ddraig68k/hardware/ddraig-libs/CAD/Connectors/35RAPC4BHN2.step

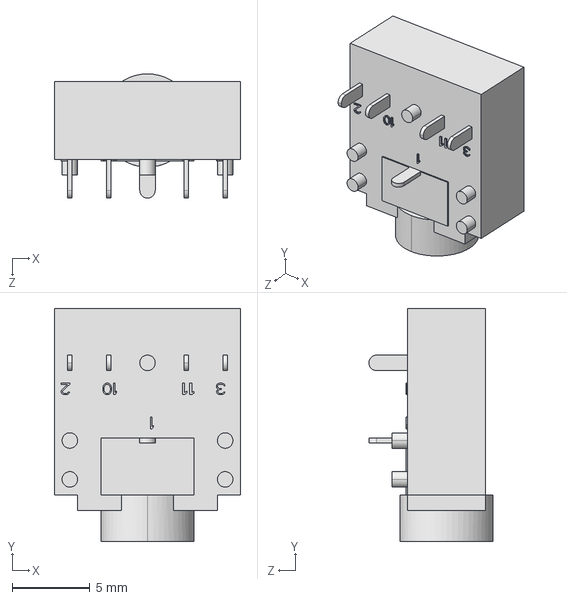
[picture p23: CAD file, 2024-05-17]
ddraig-libs/CAD/Connectors/35RAPC4BHN2.step
12.0 x 15.0 x 8.00 mm
