ddraig68k/hardware/ddraig-libs/CAD/IC Sockets/plcc44_p1-27_l16-66_w16-66.stp

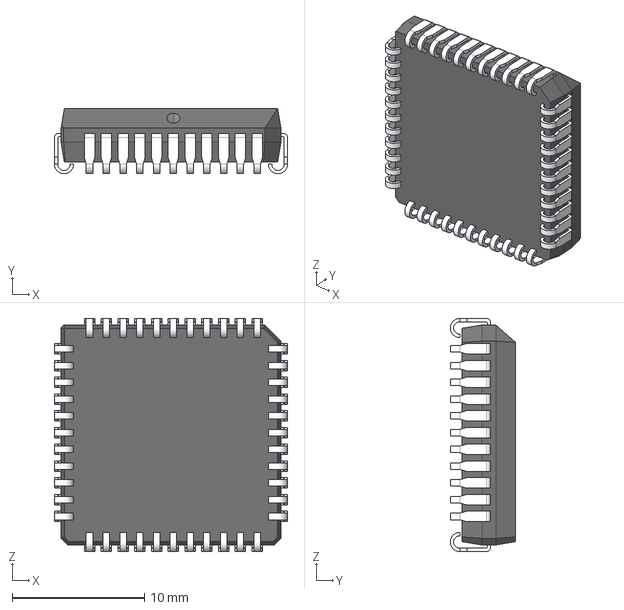
[picture p24: CAD file, 2021-05-24]
ddraig-libs/CAD/IC Sockets/plcc44_p1-27_l16-66_w16-66.stp
17.6 x 4.96 x 17.6 mm
