ddraig68k/hardware/ddraig-libs/CAD/Jumpers/Jumper3-yellow.step

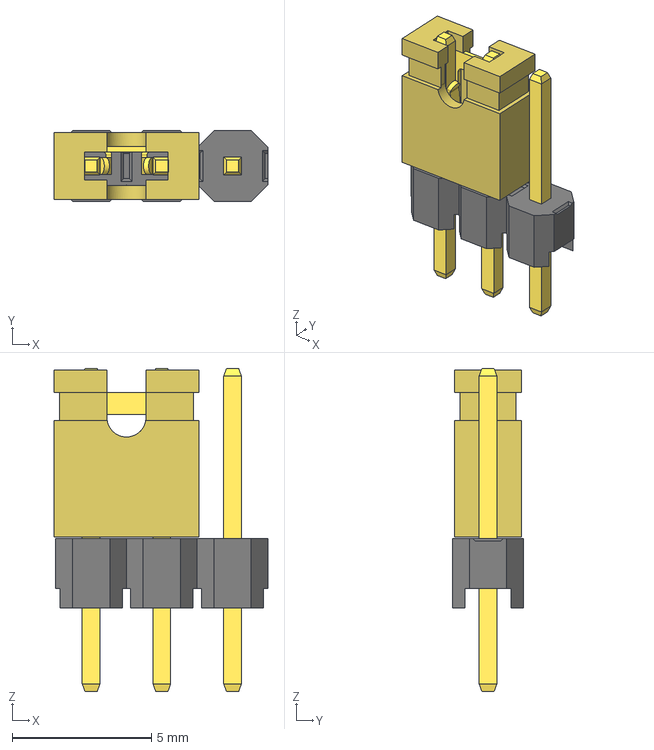
[picture p25: CAD file, 2023-10-23]
ddraig-libs/CAD/Jumpers/Jumper3-yellow.step
7.68 x 2.54 x 11.6 mm
