ddraig68k/hardware/ddraig-libs/CAD/Connectors/HARTING 09651626812.stp

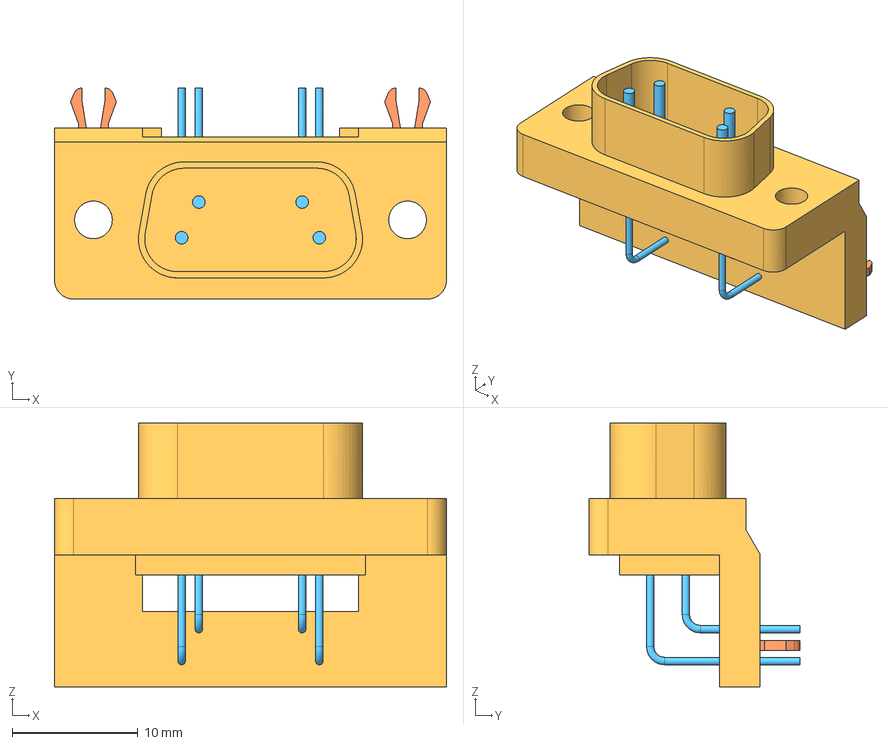
[picture p26: CAD file, 2022-08-17]
ddraig-libs/CAD/Connectors/HARTING 09651626812.stp
31.2 x 16.8 x 21.0 mm
