ddraig68k/hardware/ddraig-libs/CAD/IC Sockets/plcc84_p1-27_l29-41_w29-41.stp

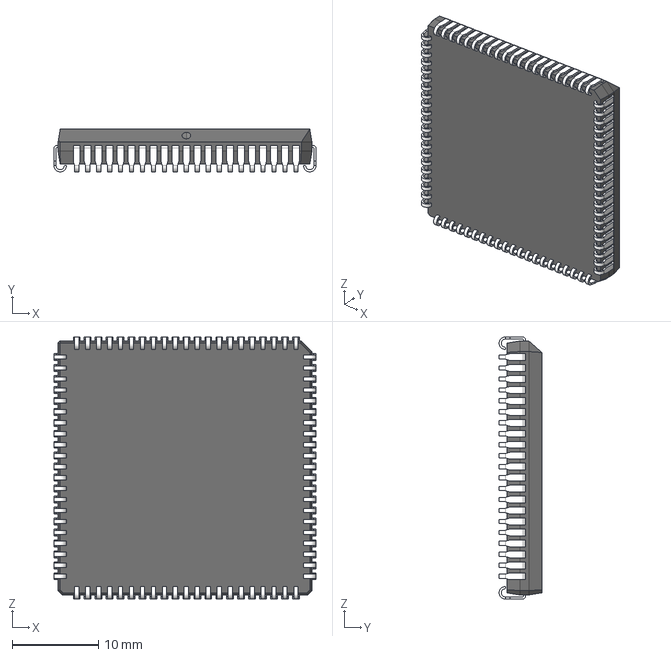
[picture p27: CAD file, 2021-05-19]
ddraig-libs/CAD/IC Sockets/plcc84_p1-27_l29-41_w29-41.stp
30.4 x 4.96 x 30.4 mm
