ddraig68k/hardware/ddraig-libs/CAD/Components/M2022TXW41-DA.stp

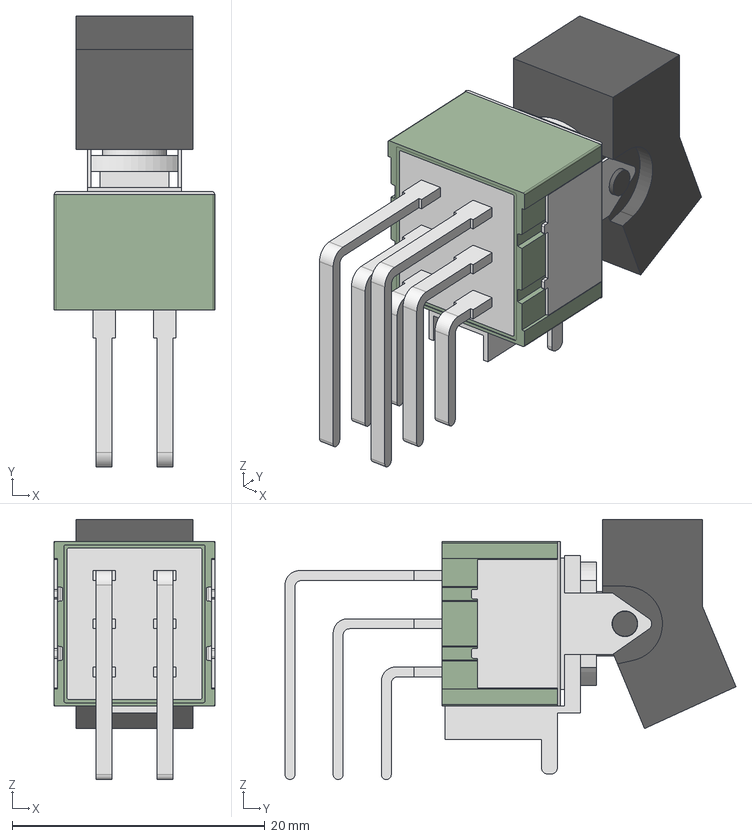
[picture p28: CAD file, 2021-09-19]
ddraig-libs/CAD/Components/M2022TXW41-DA.stp
12.7 x 35.7 x 20.6 mm
_M202TX241-switch
_M202TX-cover
_M202TX41-cover-t
_M2012TXW41-DA-terminal41
_AT4148-2A-rocker
_M202241W-terminal
