ddraig68k/hardware/ddraig-libs/CAD/Connectors/CUI_DEVICES_UP2-AH-1-TH.step

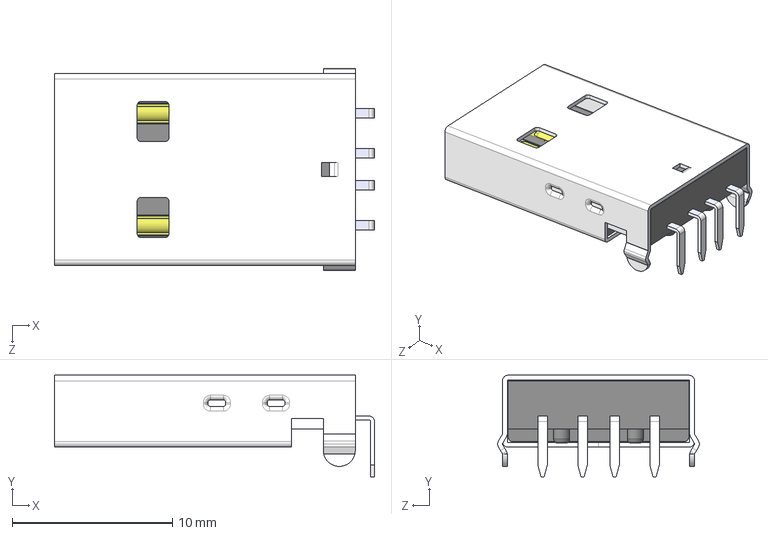
[picture p29: CAD file, 2021-10-08]
ddraig-libs/CAD/Connectors/CUI_DEVICES_UP2-AH-1-TH.step
20.0 x 6.35 x 12.6 mm
