ddraig68k/hardware/ddraig-libs/CAD/IC Sockets/PLCC44 Socket.igs

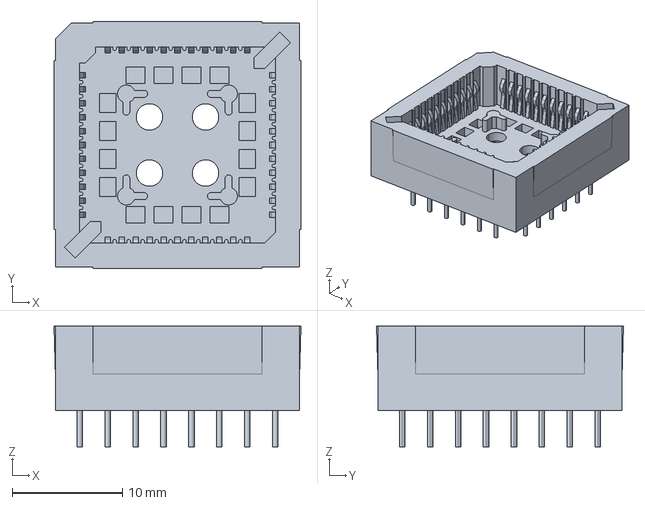
[picture p30: CAD file, 2021-05-13]
ddraig-libs/CAD/IC Sockets/PLCC44 Socket.igs
22.5 x 22.5 x 11.0 mm
