ddraig68k/hardware/ddraig-libs/CAD/ICs/XC6SLX9-2FTG256C.STEP

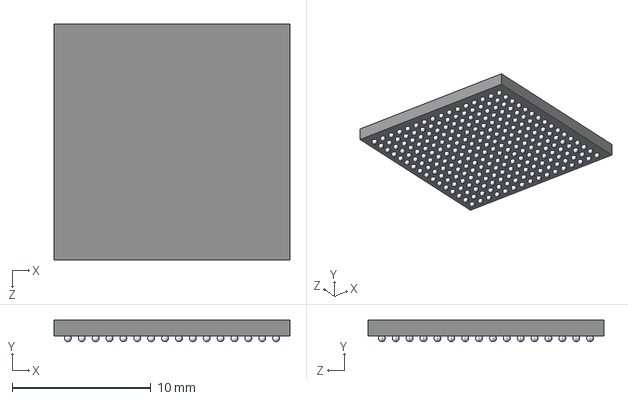
[picture p31: CAD file, 2025-01-11]
ddraig-libs/CAD/ICs/XC6SLX9-2FTG256C.STEP
17.0 x 1.55 x 17.0 mm
