ddraig68k/hardware/ddraig-libs/CAD/Components/MAX3420EECJ_.step

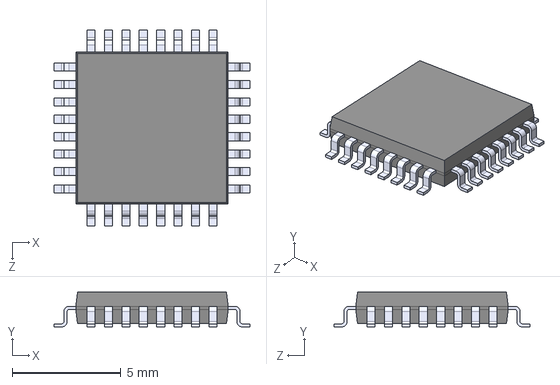
[picture p32: CAD file, 2021-08-29]
ddraig-libs/CAD/Components/MAX3420EECJ_.step
9.00 x 1.60 x 9.00 mm
