ddraig68k/hardware/ddraig-libs/CAD/Connectors/db9m.STEP

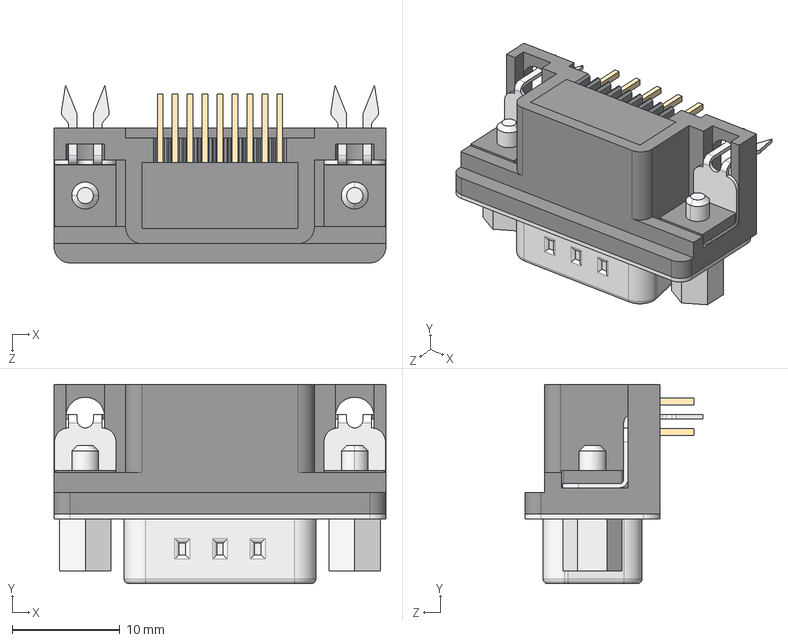
[picture p33: CAD file, 2021-10-08]
ddraig-libs/CAD/Connectors/db9m.STEP
30.8 x 18.5 x 16.5 mm
Assem1_Insulator;Insulator
Assem1_Pin_short;Pin_short
Assem1_Pin_short;Pin_short_2
Assem1_Pin_short;Pin_short_3
Assem1_Pin_short;Pin_short_4
Assem1_Pin_long;Pin_long
Assem1_Pin_long;Pin_long_2
Assem1_Pin_long;Pin_long_3
Assem1_Pin_long;Pin_long_4
Assem1_Pin_long;Pin_long_5
Assem1_Shielding;Shielding
Assem1_Insulator_2;Insulator_2
Assem1_lock;lock
Assem1_lock;lock_2
Assem1_female screw thread;female screw thread
Assem1_female screw thread;female screw thread_2
Assem1_screw;screw
Assem1_screw;screw_2
