ddraig68k/hardware/ddraig-libs/CAD/Components/ECS-3963-BN-TR.step

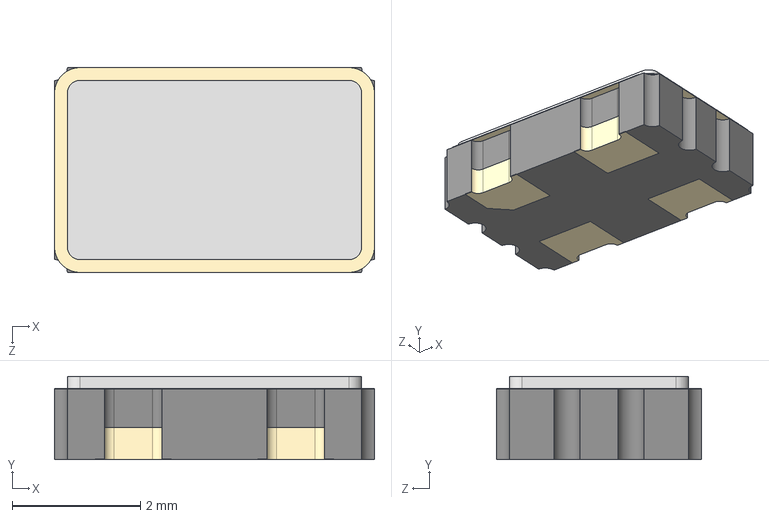
[picture p34: CAD file, 2021-08-25]
ddraig-libs/CAD/Components/ECS-3963-BN-TR.step
5.00 x 1.30 x 3.20 mm
