ddraig68k/hardware/ddraig-libs/CAD/Connectors/USB1125-GF-B.stp

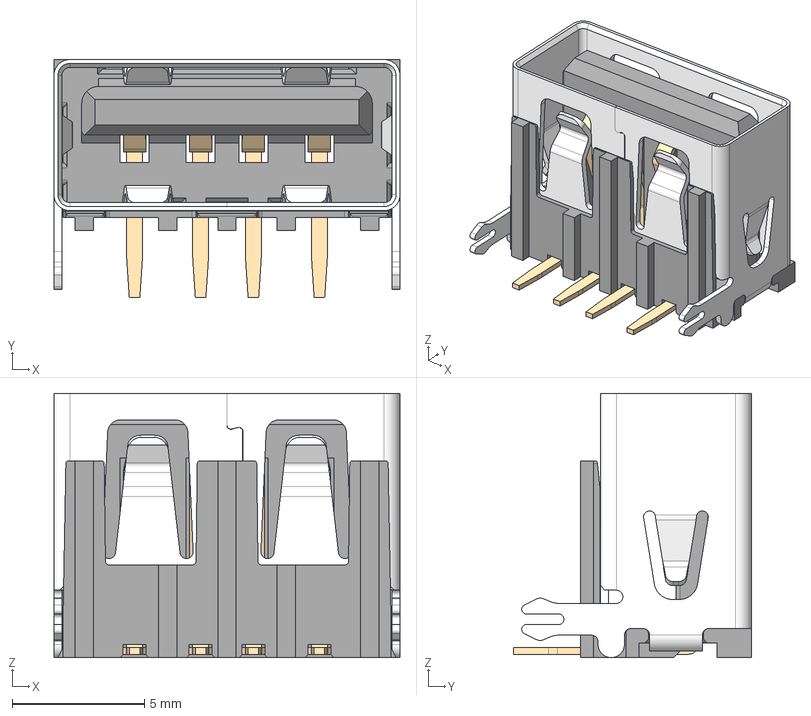
[picture p35: CAD file, 2021-10-08]
ddraig-libs/CAD/Connectors/USB1125-GF-B.stp
13.1 x 9.01 x 10.0 mm
КдИл1 x 6
