ddraig68k/hardware/ddraig-libs/CAD/ICs/SN74LS125ADR.step

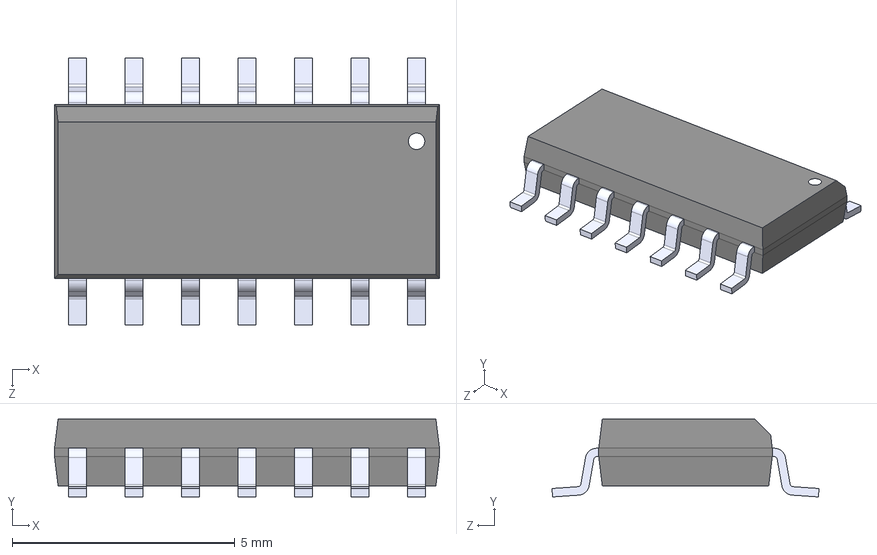
[picture p36: CAD file, 2025-01-11]
ddraig-libs/CAD/ICs/SN74LS125ADR.step
8.65 x 1.75 x 6.00 mm
