ddraig68k/hardware/ddraig-libs/CAD/Components/SN74LVC8T245PWR.step

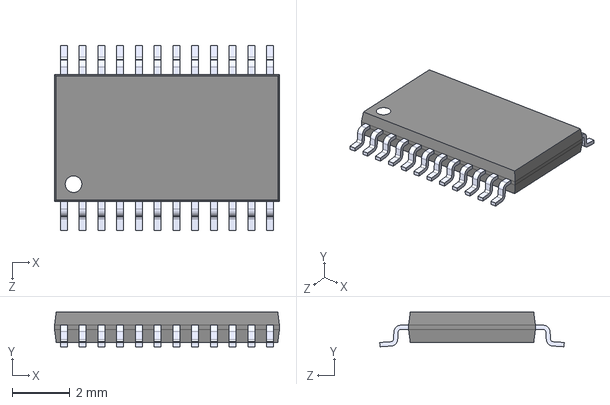
[picture p37: CAD file, 2021-08-21]
ddraig-libs/CAD/Components/SN74LVC8T245PWR.step
7.80 x 1.20 x 6.40 mm
