ddraig68k/hardware/ddraig-libs/CAD/ICs/PLCC52.STEP

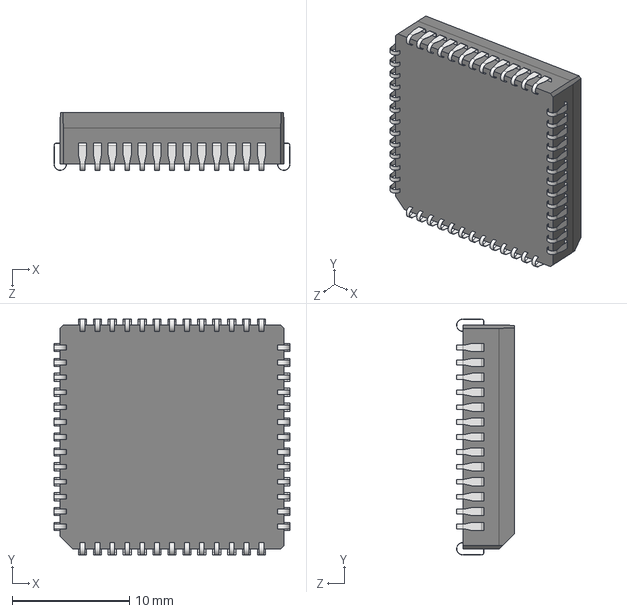
[picture p38: CAD file, 2024-05-17]
ddraig-libs/CAD/ICs/PLCC52.STEP
20.1 x 20.1 x 4.93 mm
