ddraig68k/hardware/ddraig-libs/CAD/Components/SOT230P700X180-4N.step

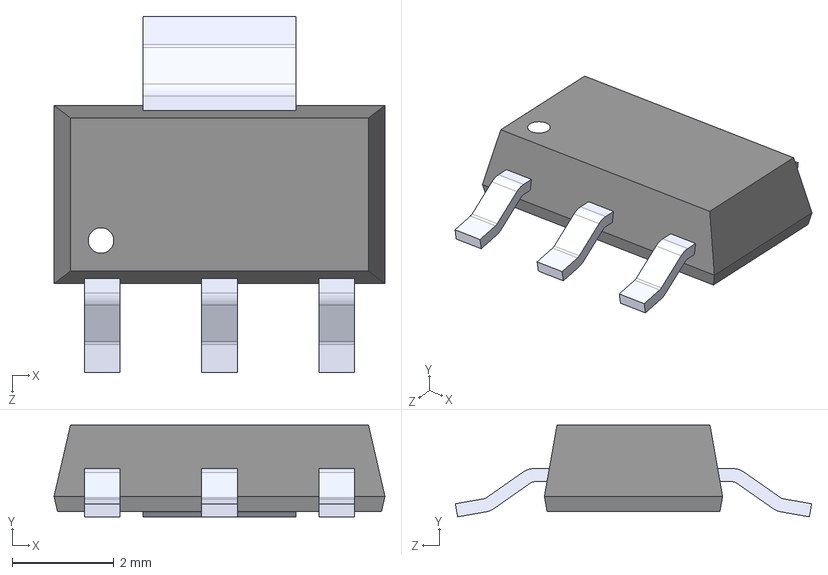
[picture p39: CAD file, 2021-08-21]
ddraig-libs/CAD/Components/SOT230P700X180-4N.step
6.50 x 1.80 x 7.00 mm
