ddraig68k/hardware/ddraig-libs/CAD/ICs/PLCC84.step

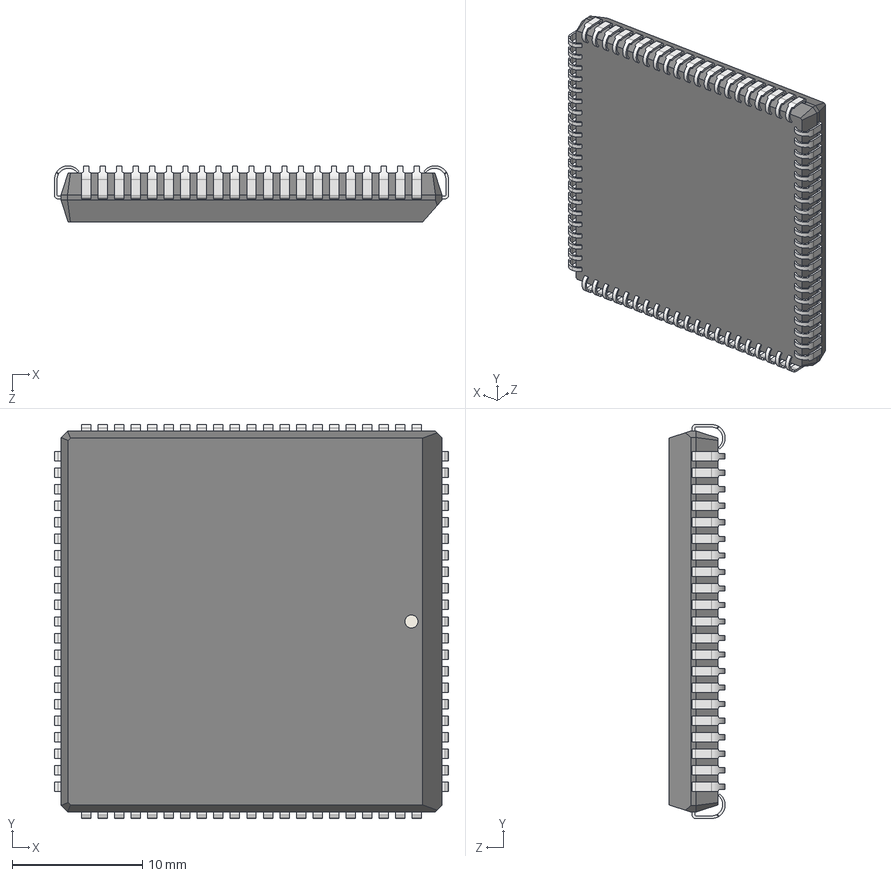
[picture p40: CAD file, 2024-05-17]
ddraig-libs/CAD/ICs/PLCC84.step
30.3 x 30.3 x 4.34 mm
