ddraig68k/hardware/ddraig-libs/CAD/Components/IS61WV102416FBLL-10TLI.stp

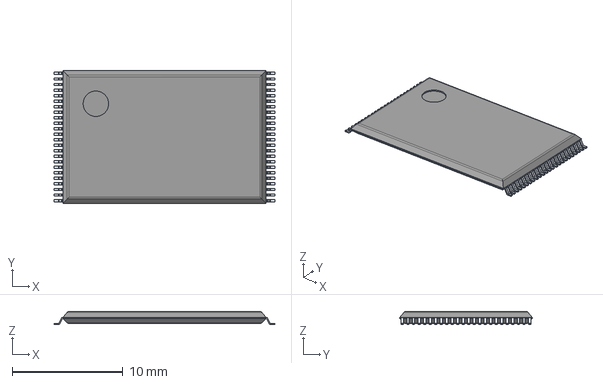
[picture p41: CAD file, 2021-08-21]
ddraig-libs/CAD/Components/IS61WV102416FBLL-10TLI.stp
20.0 x 12.0 x 1.20 mm
PinsArrayLR
