ddraig68k/hardware/ddraig-libs/CAD/ICs/PLCC44.STEP

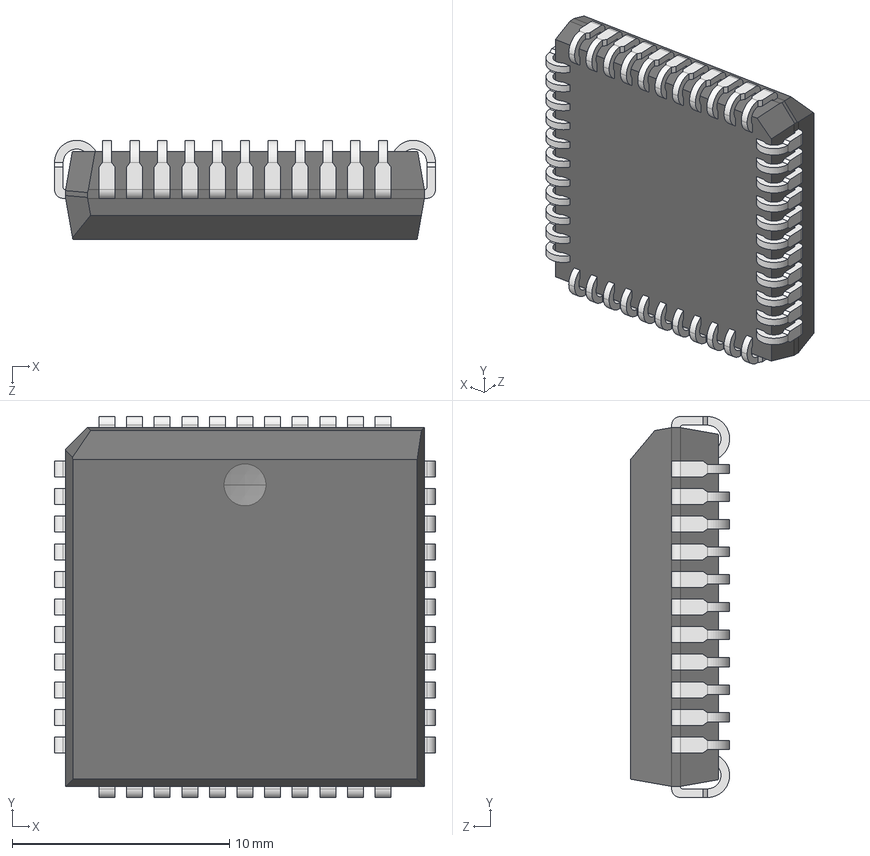
[picture p42: CAD file, 2024-05-17]
ddraig-libs/CAD/ICs/PLCC44.STEP
17.5 x 17.5 x 4.57 mm
