ddraig68k/hardware/ddraig-libs/CAD/Components/DOUBLE POTENTIOMETER.stp

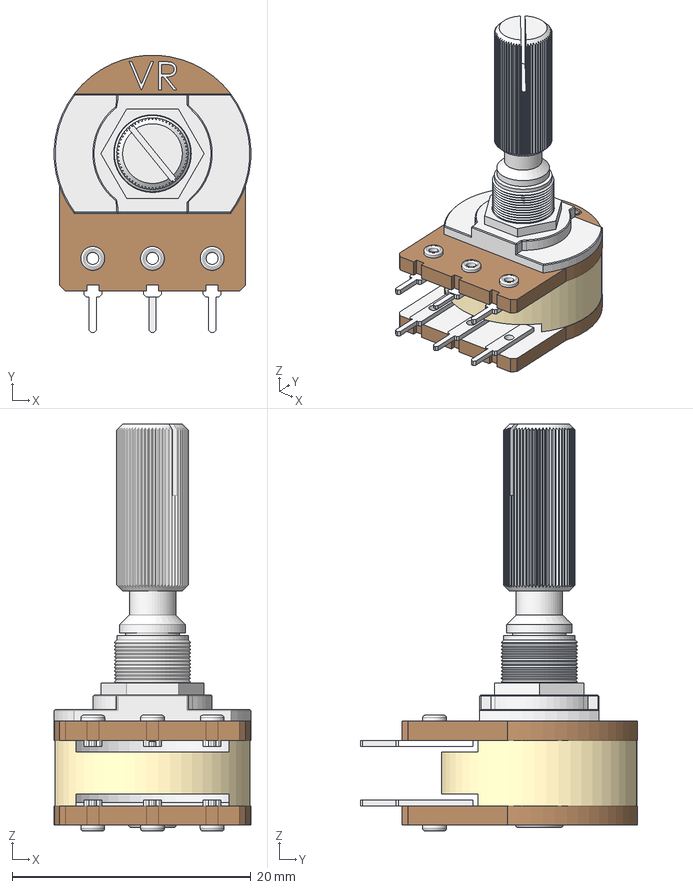
[picture p43: CAD file, 2021-06-22]
ddraig-libs/CAD/Components/DOUBLE POTENTIOMETER.stp
16.5 x 23.2 x 34.1 mm
