ddraig68k/hardware/ddraig-libs/CAD/Connectors/MEM2067-02-180-00-A_REVB.step

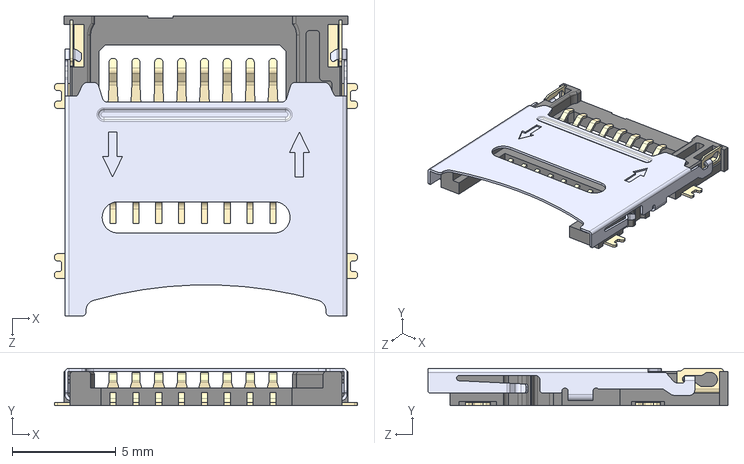
[picture p44: CAD file, 2021-09-19]
ddraig-libs/CAD/Connectors/MEM2067-02-180-00-A_REVB.step
14.6 x 1.80 x 14.5 mm
