ddraig68k/hardware/ddraig-libs/CAD/ICs/XC6SLX9-2TQG144C.step

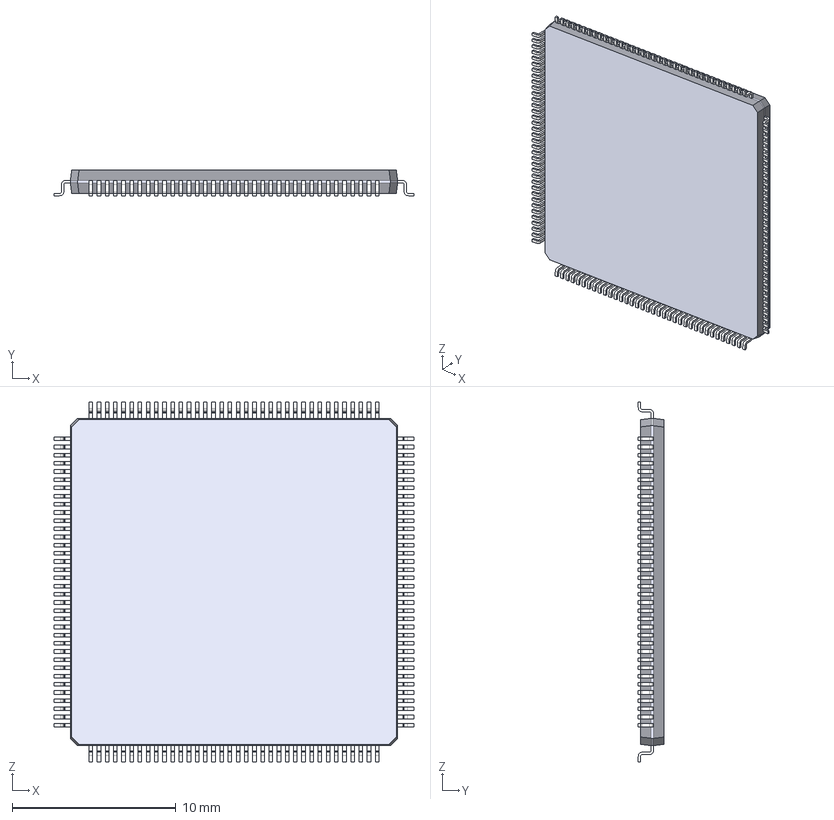
[picture p45: CAD file, 2023-11-22]
ddraig-libs/CAD/ICs/XC6SLX9-2TQG144C.step
22.0 x 1.60 x 22.0 mm
XC95144XL-10TQG144C
XC95144XL-10TQG144C001
XC95144XL-10TQG144C002
XC95144XL-10TQG144C003
XC95144XL-10TQG144C004
XC95144XL-10TQG144C005
XC95144XL-10TQG144C006
XC95144XL-10TQG144C007
XC95144XL-10TQG144C008
XC95144XL-10TQG144C009
XC95144XL-10TQG144C010
XC95144XL-10TQG144C011
XC95144XL-10TQG144C012
XC95144XL-10TQG144C013
XC95144XL-10TQG144C014
XC95144XL-10TQG144C015
XC95144XL-10TQG144C016
XC95144XL-10TQG144C017
XC95144XL-10TQG144C018
XC95144XL-10TQG144C019
XC95144XL-10TQG144C020
XC95144XL-10TQG144C021
XC95144XL-10TQG144C022
XC95144XL-10TQG144C023
XC95144XL-10TQG144C024
XC95144XL-10TQG144C025
XC95144XL-10TQG144C026
XC95144XL-10TQG144C027
XC95144XL-10TQG144C028
XC95144XL-10TQG144C029
XC95144XL-10TQG144C030
XC95144XL-10TQG144C031
XC95144XL-10TQG144C032
XC95144XL-10TQG144C033
XC95144XL-10TQG144C034
XC95144XL-10TQG144C035
XC95144XL-10TQG144C036
XC95144XL-10TQG144C037
XC95144XL-10TQG144C038
XC95144XL-10TQG144C039
XC95144XL-10TQG144C040
XC95144XL-10TQG144C041
XC95144XL-10TQG144C042
XC95144XL-10TQG144C043
XC95144XL-10TQG144C044
XC95144XL-10TQG144C045
XC95144XL-10TQG144C046
XC95144XL-10TQG144C047
XC95144XL-10TQG144C048
XC95144XL-10TQG144C049
XC95144XL-10TQG144C050
XC95144XL-10TQG144C051
XC95144XL-10TQG144C052
XC95144XL-10TQG144C053
XC95144XL-10TQG144C054
XC95144XL-10TQG144C055
XC95144XL-10TQG144C056
XC95144XL-10TQG144C057
XC95144XL-10TQG144C058
XC95144XL-10TQG144C059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
