ddraig68k/hardware/ddraig-libs/CAD/Components/AOCJY1.STEP

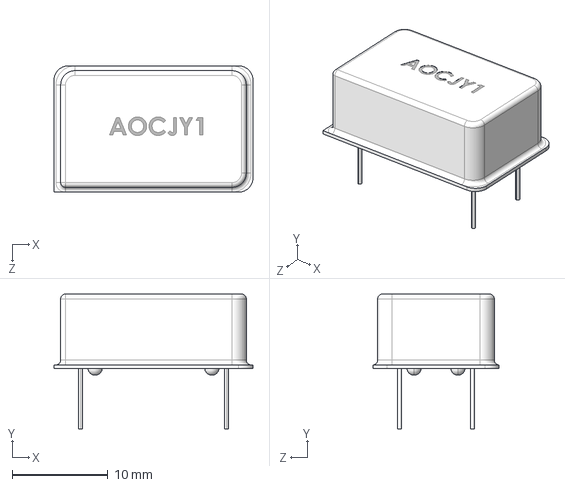
[picture p46: CAD file, 2021-05-19]
ddraig-libs/CAD/Components/AOCJY1.STEP
20.8 x 14.1 x 13.2 mm
