ddraig68k/hardware/ddraig-libs/CAD/Connectors/57PC5F.step

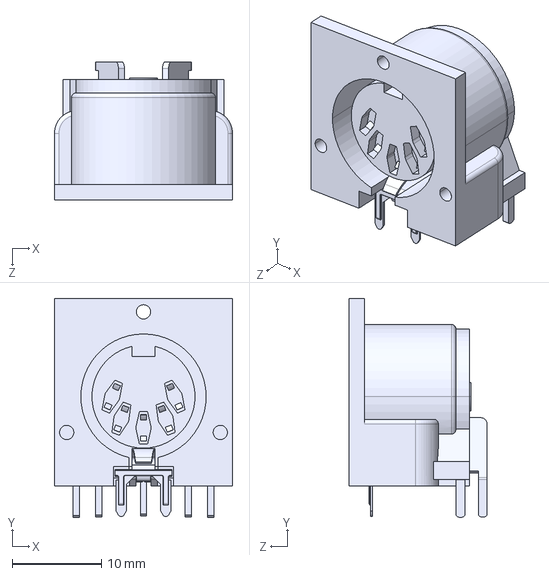
[picture p47: CAD file, 2021-08-29]
ddraig-libs/CAD/Connectors/57PC5F.step
20.0 x 24.5 x 15.5 mm
