ddraig68k/hardware/ddraig-libs/CAD/ICs/plcc68_p1-27_l24-33_w24-33.stp

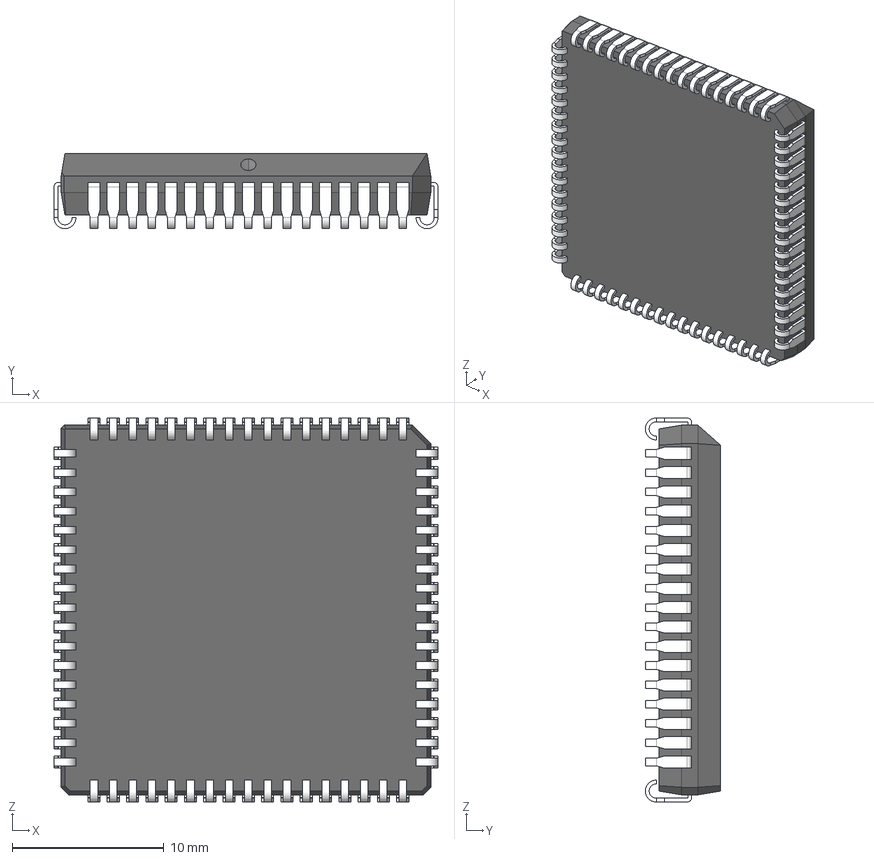
[picture p48: CAD file, 2022-08-17]
ddraig-libs/CAD/ICs/plcc68_p1-27_l24-33_w24-33.stp
25.3 x 4.96 x 25.3 mm
