ddraig68k/hardware/ddraig-libs/CAD/Components/AIUR-02H.STEP

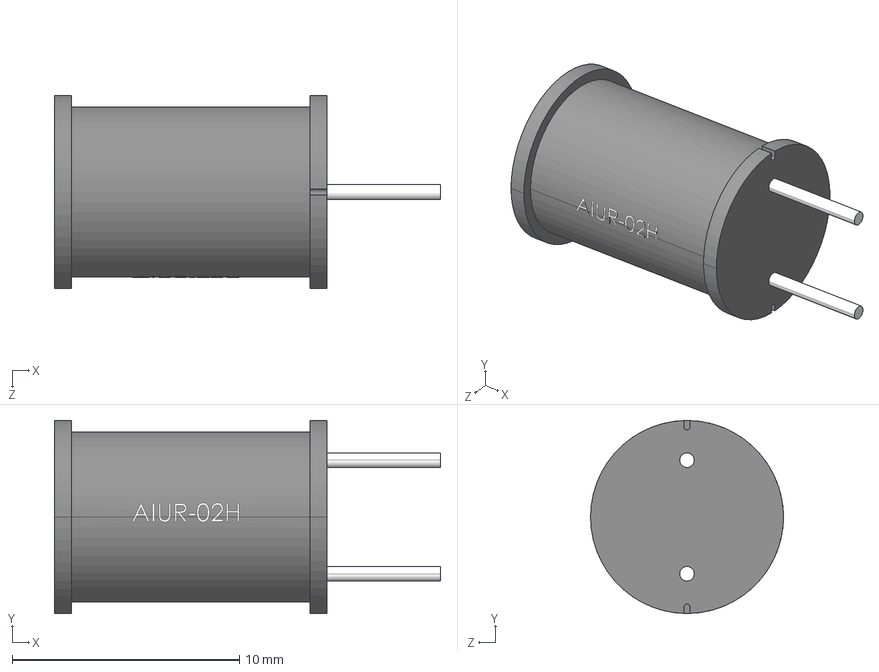
[picture p49: CAD file, 2021-05-19]
ddraig-libs/CAD/Components/AIUR-02H.STEP
17.0 x 8.50 x 8.50 mm
