ddraig68k/hardware/ddraig-libs/CAD/Connectors/9-211509-0.stp

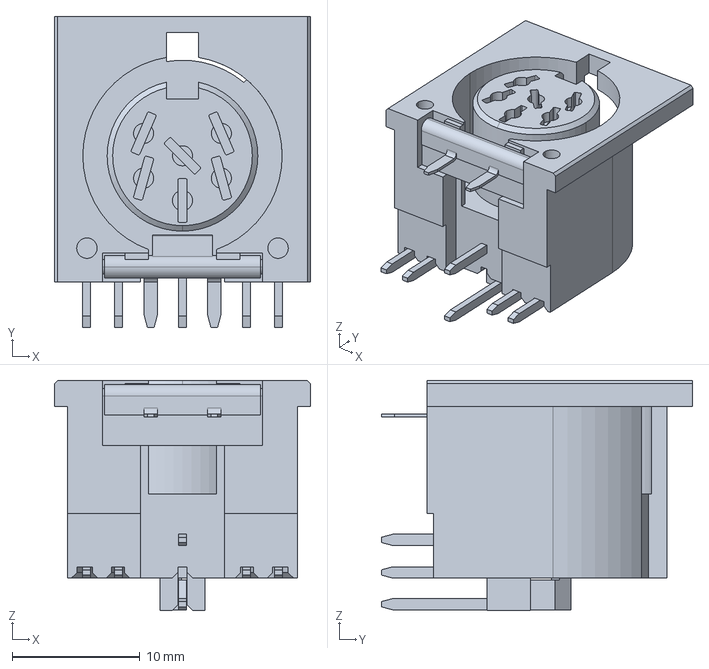
[picture p50: CAD file, 2021-08-29]
ddraig-libs/CAD/Connectors/9-211509-0.stp
20.1 x 24.4 x 18.0 mm
