ddraig68k/hardware/ddraig-libs/CAD/ICs/LTC6903CMS8PBF.step

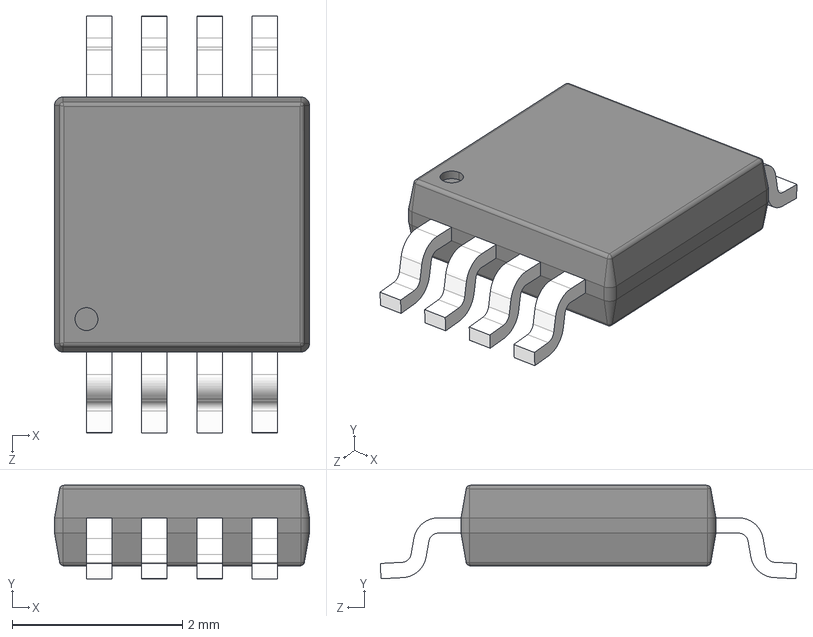
[picture p51: CAD file, 2021-07-02]
ddraig-libs/CAD/ICs/LTC6903CMS8PBF.step
3.00 x 1.10 x 4.90 mm
