ddraig68k/hardware/ddraig-libs/CAD/Components/AIUR-16.STEP

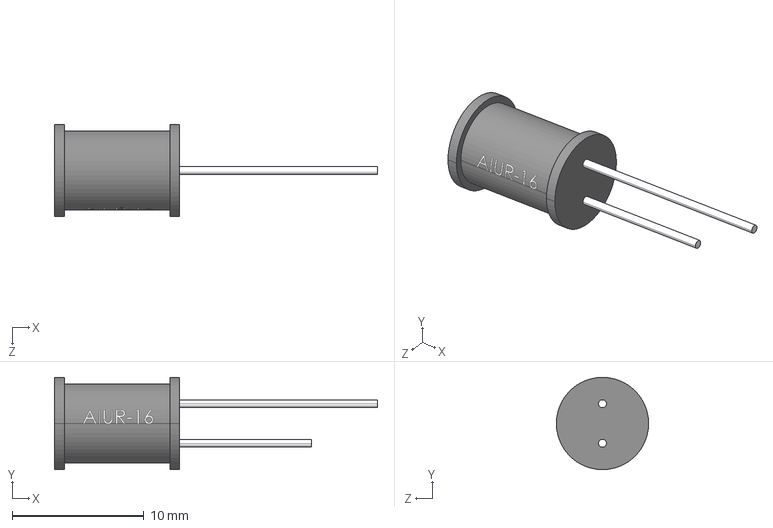
[picture p52: CAD file, 2021-05-19]
ddraig-libs/CAD/Components/AIUR-16.STEP
24.5 x 7.00 x 7.00 mm
