ddraig68k/hardware/ddraig-libs/CAD/Connectors/lumberg_tm_0508_a_04.stp

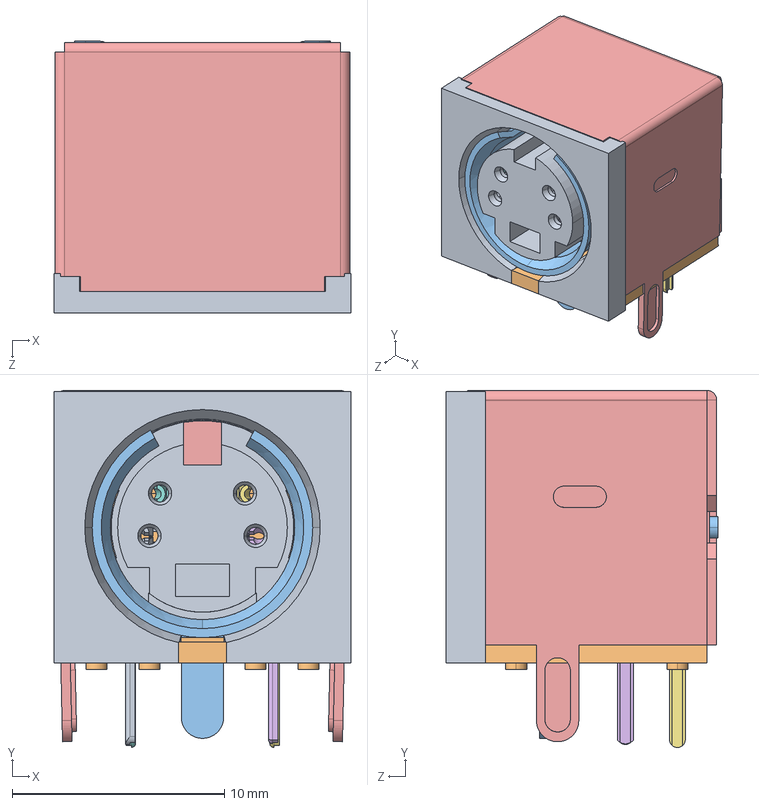
[picture p53: CAD file, 2021-07-02]
ddraig-libs/CAD/Connectors/lumberg_tm_0508_a_04.stp
14.0 x 16.8 x 12.8 mm
MJ-373 BODY 4PIN MIND-20150909
MINDHOLEBODY-20150613
NICKEL PLATED20150624
SHIELDING PLATE20150614
MDC-028-7
MDC-028-10
MDC-028-11
MDC-028-9
