ddraig68k/hardware/ddraig-libs/CAD/Components/XTAL2.STEP

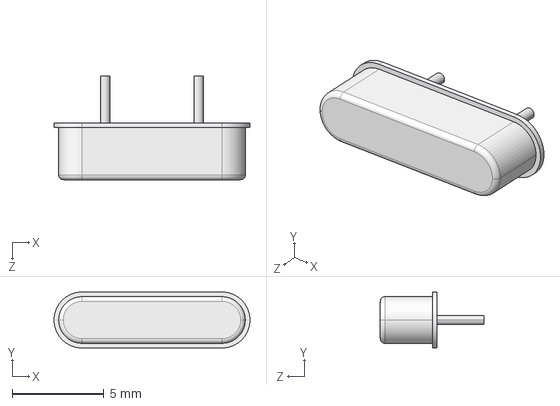
[picture p54: CAD file, 2021-05-19]
ddraig-libs/CAD/Components/XTAL2.STEP
10.7 x 3.05 x 5.63 mm
