ddraig68k/hardware/ddraig-libs/CAD/Connectors/KLPX-0848A-2-B_rA4.STEP

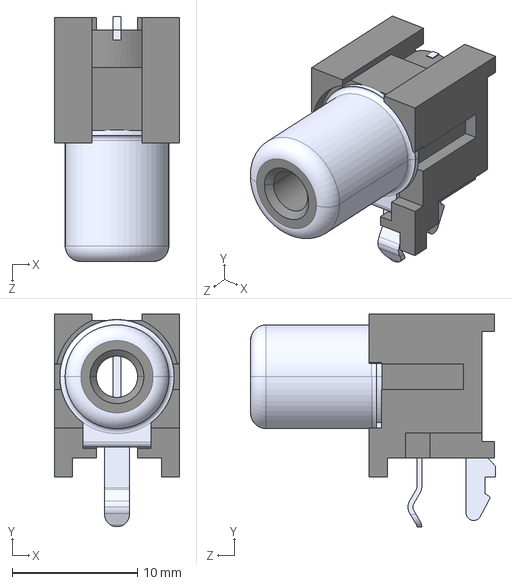
[picture p55: CAD file, 2021-07-02]
ddraig-libs/CAD/Connectors/KLPX-0848A-2-B_rA4.STEP
10.0 x 17.0 x 19.6 mm
