ddraig68k/hardware/ddraig-libs/CAD/Components/ACH.STEP

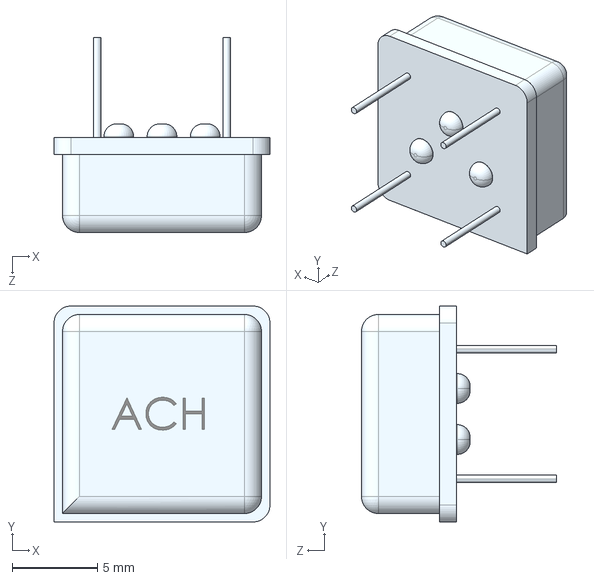
[picture p56: CAD file, 2021-05-19]
ddraig-libs/CAD/Components/ACH.STEP
12.7 x 12.7 x 11.5 mm
