ddraig68k/hardware/ddraig-libs/CAD/Connectors/c-5749268-1-a-3d.stp

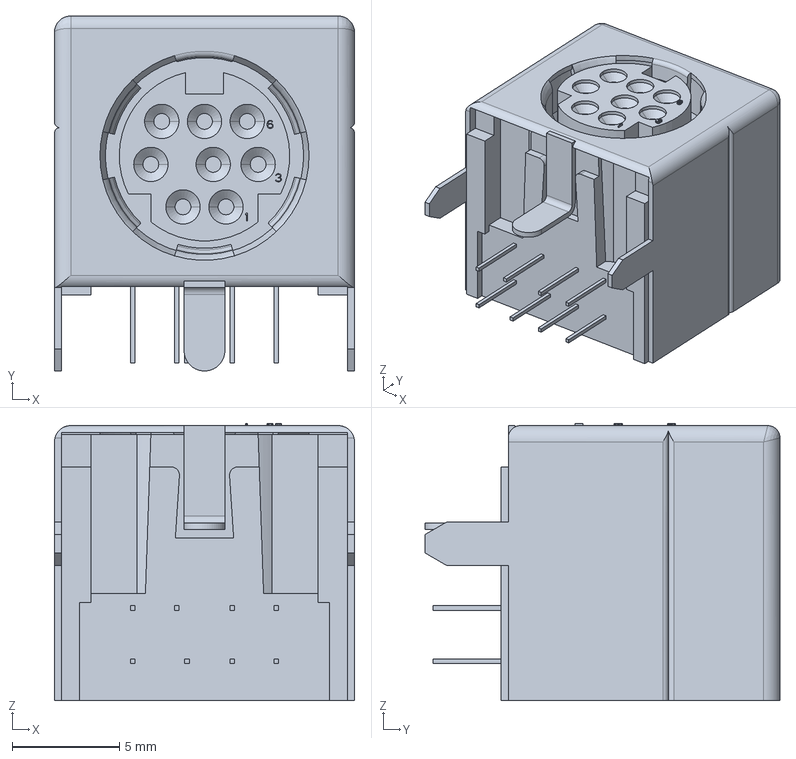
[picture p57: CAD file, 2021-07-02]
ddraig-libs/CAD/Connectors/c-5749268-1-a-3d.stp
14.0 x 16.6 x 12.9 mm
