ddraig68k/hardware/ddraig-libs/CAD/Connectors/c-0770997-01-c-3d.stp

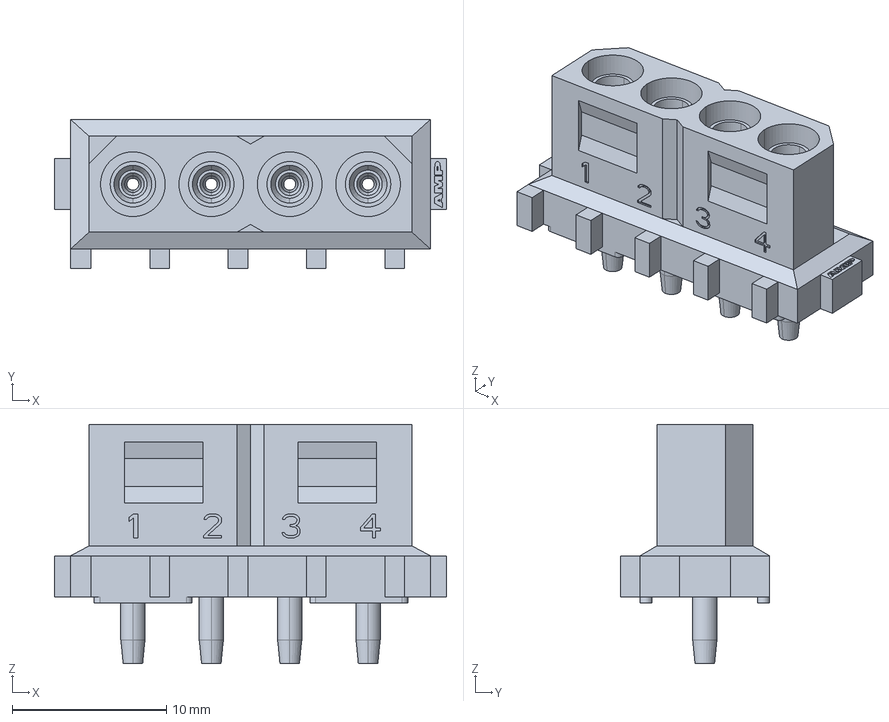
[picture p58: CAD file, 2021-05-24]
ddraig-libs/CAD/Connectors/c-0770997-01-c-3d.stp
25.4 x 9.65 x 15.5 mm
