ddraig68k/hardware/ddraig-libs/CAD/Connectors/ATX_te-1-1775099-3-e-3d.stp

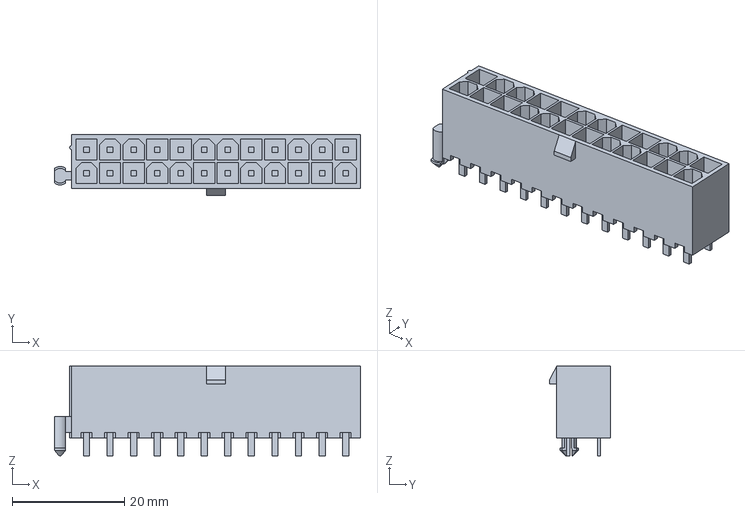
[picture p59: CAD file, 2021-03-25]
ddraig-libs/CAD/Connectors/ATX_te-1-1775099-3-e-3d.stp
54.6 x 10.9 x 16.0 mm
