ddraig68k/hardware/ddraig-libs/CAD/Connectors/MiniDin_6way.stp

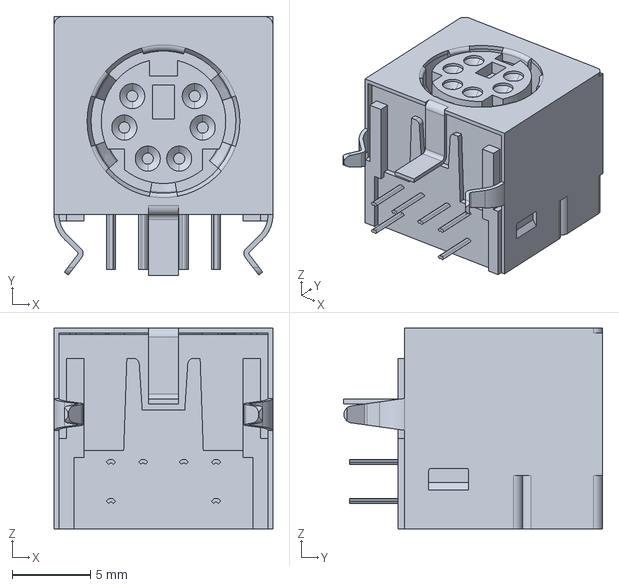
[picture p60: CAD file, 2021-03-25]
ddraig-libs/CAD/Connectors/MiniDin_6way.stp
14.0 x 16.5 x 12.8 mm
