ddraig68k/hardware/ddraig-libs/CAD/Connectors/c-5535090-9-a-3d.stp

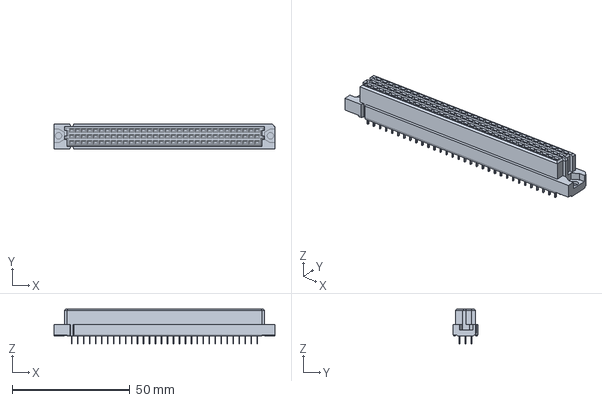
[picture p61: CAD file, 2021-03-23]
ddraig-libs/CAD/Connectors/c-5535090-9-a-3d.stp
93.9 x 10.6 x 14.8 mm
