ddraig68k/hardware/ddraig-libs/CAD/Connectors/RJMG1BD3B8K1ANR--3DModel-STEP-56544.STEP

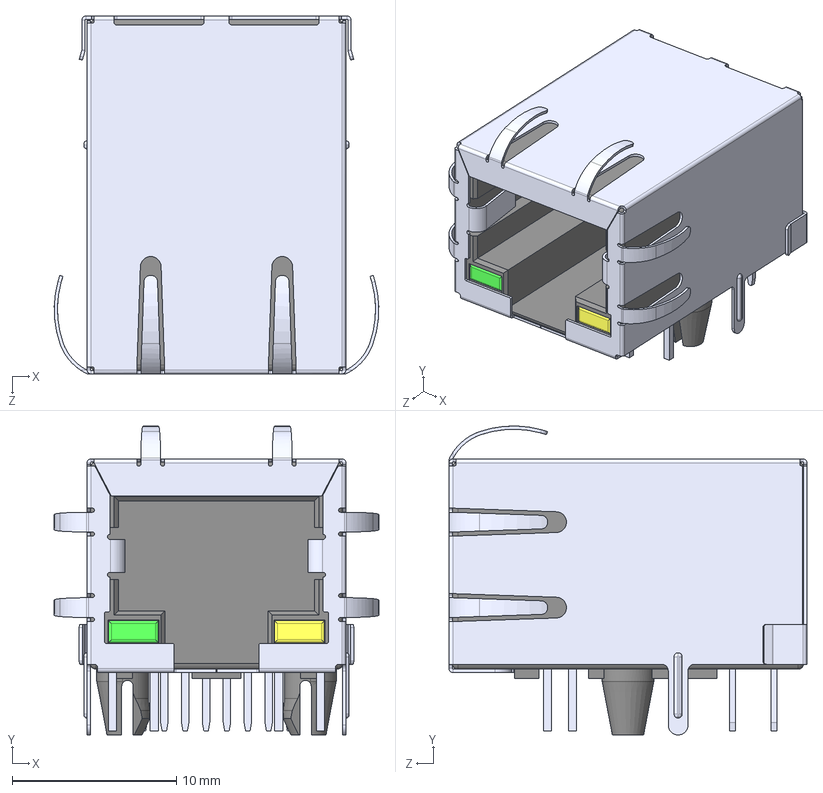
[picture p62: CAD file, 2021-03-23]
ddraig-libs/CAD/Connectors/RJMG1BD3B8K1ANR--3DModel-STEP-56544.STEP
19.7 x 18.8 x 21.8 mm
